ScatteredDrifter/Endeavour/rev3/pcb/Endeavour-2.kicad_sch

## KiCad design rev3/pcb/Endeavour-2.kicad_sch (2024-03-17)

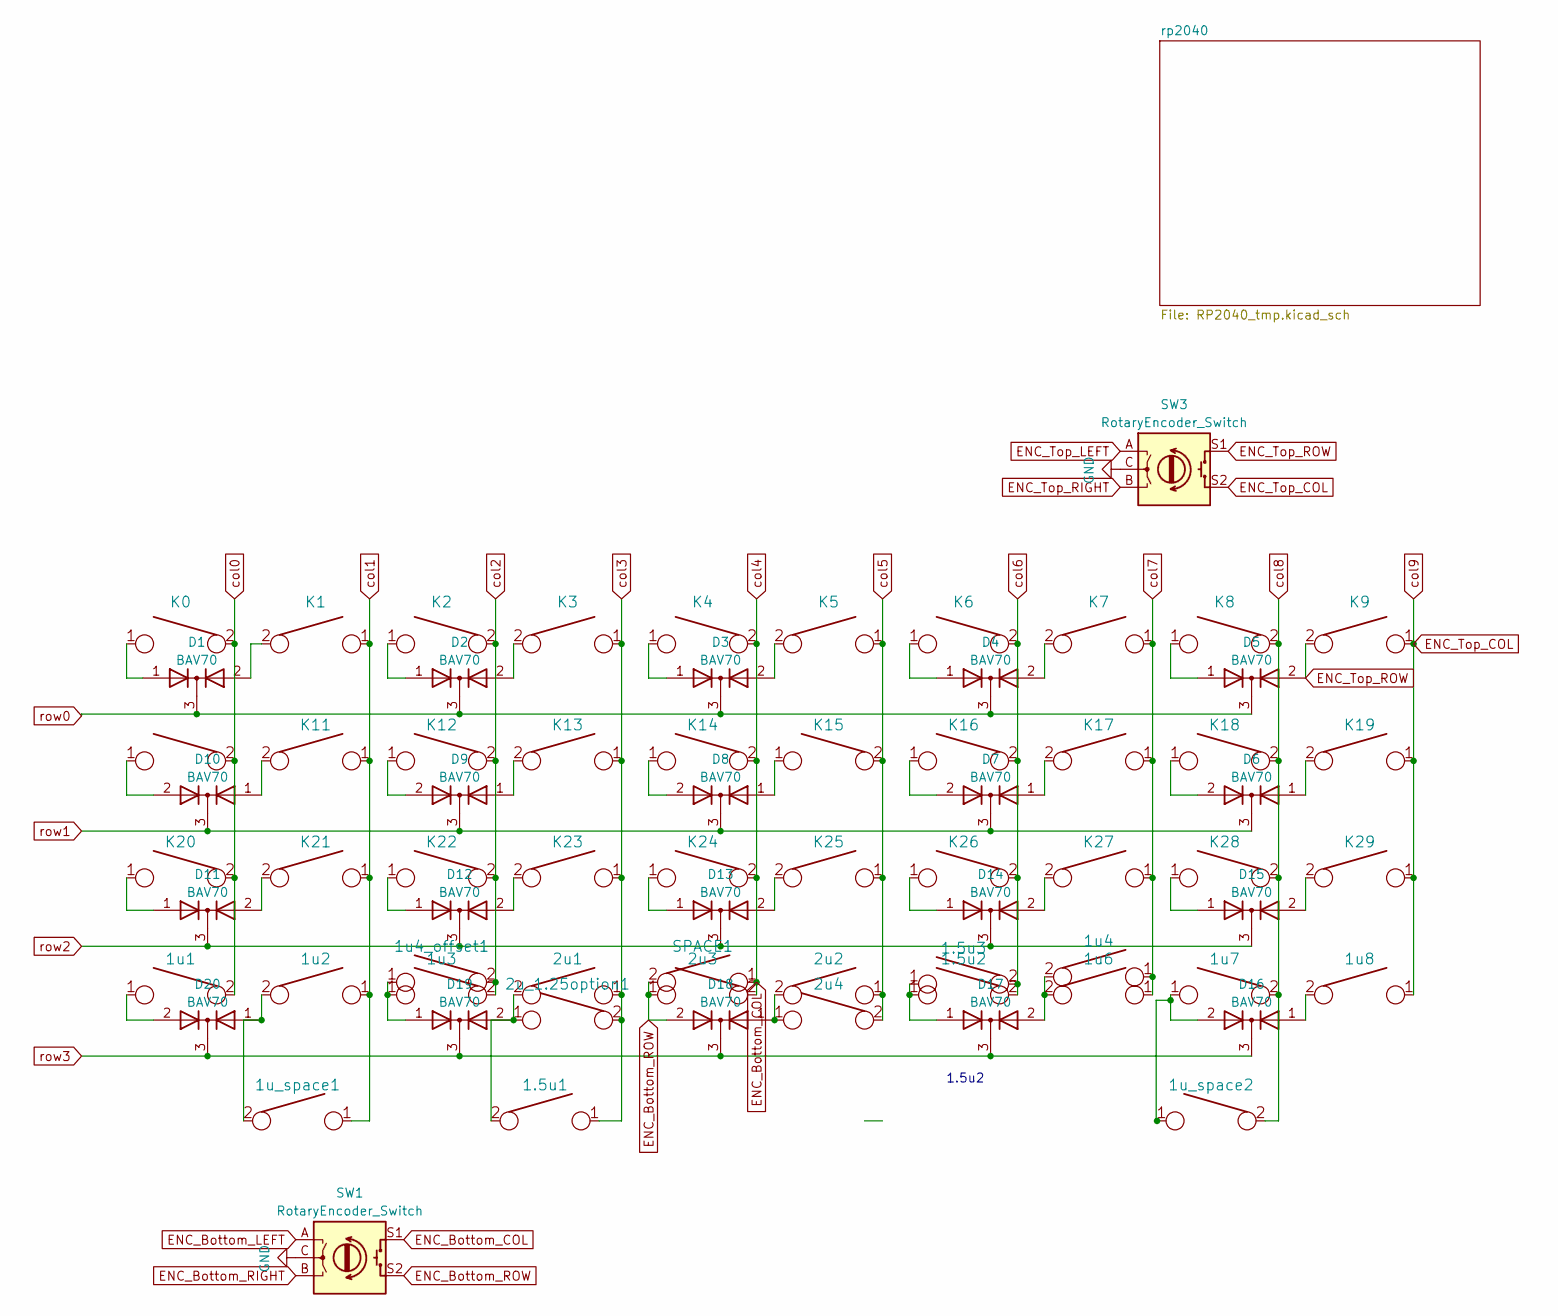
[picture p27: schematic Endeavour-2.kicad_sch]

Parts:
1.5u1, 1.5u2, 1.5u3: 1.5u; SW_MX_HS_1u_NOREF
1u1, 1u2, 1u3, 1u4, 1u4_offset1, 1u6, 1u7, 1u8, 1u_space1, 1u_space2: 1u; SW_MX_HS_1u_NOREF
2u1, 2u2, 2u3, 2u4, 2u_1.25option1: 2u; SW_MX_HS_1u_NOREF
D1, D2, D3, D4, D5, D6, D7, D8, D9, D10, D11, D12, D13, D14, D15, D16, D17, D18, D19, D20: BAV70; SOT-23; LCSC C181110
K0, K1, K2, K3, K4, K5, K6, K7, K8, K9, K10, K11, K12, K13, K14, K15, K16, K17, K18, K19, K20, K21, K22, K23, K24, K25, K26, K27, K28, K29: 1u; SW_MX_HS_1u_NOREF
SPACE1: 7u; SW_MX_HS_1u_NOREF
SW1, SW3: RotaryEncoder_Switch; ROT_Alps_EC11E-Switch

Connections:
ENC_Bottom_LEFT: SW1.A
ENC_Bottom_RIGHT: SW1.B
ENC_Bottom_ROW: 2u3.1, D18.2 (A), SPACE1.2, SW1.S2
ENC_Top_LEFT: SW3.A
ENC_Top_RIGHT: SW3.B
ENC_Top_ROW: D5.2 (A), K9.2, SW3.S1
GND: SW1.C, SW3.C
unnamed: 1.5u1.2, 2u1.2, 2u_1.25option1.1, D19.2 (A)
unnamed: 1.5u2.1, 1.5u3.1, D17.1 (A)
unnamed: 1u1.1, D20.2 (A)
unnamed: 1u2.2, 1u_space1.2, D20.1 (A)
unnamed: 1u3.1, 1u4_offset1.1, D19.1 (A)
unnamed: 1u4.2, 1u6.2, D17.2 (A)
unnamed: 1u7.1, 1u_space2.1, D16.2 (A)
unnamed: 1u8.2, D16.1 (A)
unnamed: 2u2.2, 2u4.1, D18.1 (A)
unnamed: D1.1 (A), K0.1
unnamed: D1.2 (A), K1.2
unnamed: D2.1 (A), K2.1
unnamed: D2.2 (A), K3.2
unnamed: D3.1 (A), K4.1
unnamed: D3.2 (A), K5.2
unnamed: D4.1 (A), K6.1
unnamed: D4.2 (A), K7.2
unnamed: D5.1 (A), K8.1
unnamed: D6.1 (A), K19.2
unnamed: D6.2 (A), K18.1
unnamed: D7.1 (A), K17.2
unnamed: D7.2 (A), K16.1
unnamed: D8.1 (A), K15.1
unnamed: D8.2 (A), K14.1
unnamed: D9.1 (A), K13.2
unnamed: D9.2 (A), K12.1
unnamed: D10.1 (A), K11.2
unnamed: D10.2 (A), K10.1
unnamed: D11.1 (A), K20.1
unnamed: D11.2 (A), K21.2
unnamed: D12.1 (A), K22.1
unnamed: D12.2 (A), K23.2
unnamed: D13.1 (A), K24.1
unnamed: D13.2 (A), K25.2
unnamed: D14.1 (A), K26.1
unnamed: D14.2 (A), K27.2
unnamed: D15.1 (A), K28.1
unnamed: D15.2 (A), K29.2
col0: 1u1.2, K0.2, K10.2, K20.2
col1: 1u2.1, 1u_space1.1, K1.1, K11.1, K21.1
col2: 1u3.2, 1u4_offset1.2, K2.2, K12.2, K22.2
col3: 1.5u1.1, 2u1.1, 2u_1.25option1.2, K3.1, K13.1, K23.1
col4: 2u3.2, K4.2, K14.2, K24.2, SPACE1.1, SW1.S1
col5: 2u2.1, 2u4.2, K5.1, K15.2, K25.1
col6: 1.5u2.2, 1.5u3.2, K6.2, K16.2, K26.2
col7: 1u4.1, 1u6.1, K7.1, K17.1, K27.1
col8: 1u7.2, 1u_space2.2, K8.2, K18.2, K28.2
col9: 1u8.1, K9.1, K19.1, K29.1, SW3.S2
row0: D1.3 (K), D2.3 (K), D3.3 (K), D4.3 (K), D5.3 (K)
row1: D6.3 (K), D7.3 (K), D8.3 (K), D9.3 (K), D10.3 (K)
row2: D11.3 (K), D12.3 (K), D13.3 (K), D14.3 (K), D15.3 (K)
row3: D16.3 (K), D17.3 (K), D18.3 (K), D19.3 (K), D20.3 (K)

Notes on the sheet:
1.5u2
